JeremyJStarcher/pal1-ram-rom/datasheets/overclocking_pico_files/pico.delta2average.png

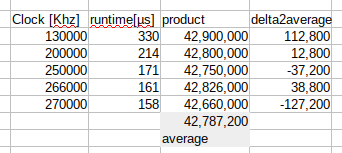
datasheets/overclocking_pico_files/pico.delta2average.png
