JeremyJStarcher/pal1-ram-rom/pics/20240308_011437.jpg

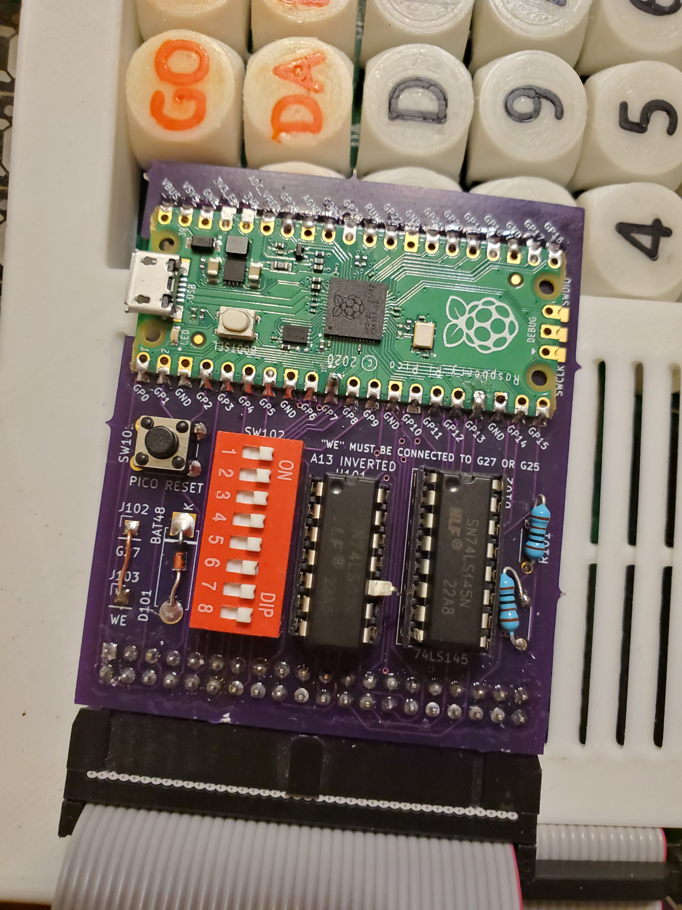
pics/20240308_011437.jpg
