JeremyJStarcher/pal1-ram-rom/datasheets/overclocking_pico_files/mc.performance.png

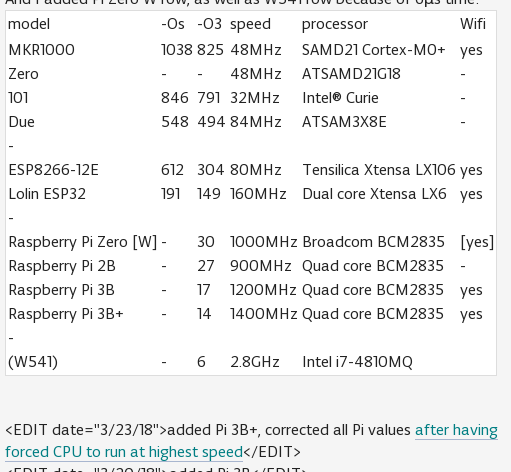
datasheets/overclocking_pico_files/mc.performance.png
