JeremyJStarcher/pal1-ram-rom/src/pal-expansion/commands.c

#include "commands.h"

#include <ctype.h>
#include <hardware/clocks.h>
#include <hardware/flash.h>
#include <hardware/sync.h>
#include <hardware/timer.h>
#include <malloc.h>
#include <pico/multicore.h>
#include <pico/stdlib.h>
#include <stdarg.h>
#include <stdbool.h>
#include <stdio.h>
#include <stdlib.h>
#include <string.h>
#include <tusb.h>

#include "clockspeed.h"
#include "rambuf.h"
#include "xmodem.h"

#define MEMORY_UNMAPPED 0
#define MEMORY_RAM 1
#define MEMORY_ROM 2
#define MEMORY_IGNORE 3
#define MEMORY_UNKNOWN 4

#define MAX_VALID_INDEX ((_flash_size / 2) / sizeof(SysStateStruct)) - 1

//#define PRINT_DEBUG

#define TOKEN_RAM 1
#define TOKEN_ROM 2
#define TOKEN_UNKNOWN 3

void main_memory_loop(void);

unsigned long _xip_base;
unsigned long _flash_size;
uint32_t ints;

bool load_ptp_error = false;
bool load_ptp_done = false;

// If the PAL is not responding, stop sending things to it.
bool output_to_pal = true;

#include <stdarg.h>
#include <stdio.h>

void aputchar(char c) {
  putchar(c);

  if (output_to_pal) {
    pokeram(XCH_TO_PAL, c);
    pokeram(XCH_CMD_REG, XCH_CMD_CHOUT);

    absolute_time_t start_time = get_absolute_time();

    while (true) {
      int xch_clk = peekram(XCH_CMD_REG);
      if (xch_clk == XCH_CMD_NONE) {
        break;
      }

      if (absolute_time_diff_us(start_time, get_absolute_time()) >= 500000) {
        output_to_pal = false;
        break;
      }
    }
  }
}

void aputs(char *c) {
  for (int i = 0; i < strlen(c); ++i) {
    aputchar(c[i]);
  }

  aputchar('\r');
  aputchar('\n');
}

// Wrapper function for snaprintf to send formatted string via api_send_char.
int aprintf(const char *format, ...) {
  va_list args;
  va_start(args, format);

  // Assuming a maximum buffer size. Adjust this according to your needs.
  char buffer[1024];
  int formatted_len = vsnprintf(buffer, sizeof(buffer), format, args);
  va_end(args);

  // Check if snaprintf succeeded
  if (formatted_len < 0) {
    return -1;  // Return an error.
  }

  // Send each character of the formatted string via the API.
  for (int i = 0; i < formatted_len; ++i) {
    aputchar(buffer[i]);
  }

  return formatted_len;  // Return the number of characters sent.
}

uint8_t token_ram_rom(char *token) {
  if (strcmp(token, "ROM") == 0) {
    return TOKEN_ROM;
  }

  if (strcmp(token, "RAM") == 0) {
    return TOKEN_RAM;
  }

  return TOKEN_UNKNOWN;
}

void pause() {
  // If the USB is still busy when we enter a critical section,
  // bad things tend to happen, so give time for the USB bursts to
  // to through.

  volatile long long i;
  long long count = 1 * 10000000;

  for (i = 0; i < count; i++) {
    // Empty loop body
  }
}

uintptr_t get_offset(size_t index) {
  // Assuming you want the size of the structure
  size_t size = sizeof(SysStateStruct);
  return (_flash_size / 2) + (index * size);
}

bool is_safe_to_access(size_t index) {
  if (index > MAX_VALID_INDEX) {
    return false;  // Index is out of valid range
  }

  uintptr_t offset = get_offset(index);
  uintptr_t end_address = XIP_BASE + offset + sizeof(SysStateStruct);
  // Check if end address exceeds flash size or other boundary conditions
  if (end_address > XIP_BASE + _flash_size) {
    return false;
  }

  // Add any additional checks for alignment here if necessary
  // For example, if your system requires 4-byte alignment:
  if ((XIP_BASE + offset) % (4 * 1024) != 0) {
    return false;  // Address is not properly aligned
  }

  return true;  // Safe to access
}

SysStateStruct *get_slot_ptr(size_t index) {
  if (!is_safe_to_access(index)) {
    aprintf("Error: Unsafe to access the requested memory slot.\r\n");
    return NULL;  // Use NULL for pointer error signaling
  }

  size_t size = sizeof(SysStateStruct);
  uintptr_t offset = get_offset(index);

  // Correctly cast and return the pointer
  return (SysStateStruct *)(XIP_BASE + offset);
}

void load_slot_command(char *token) {
  char *param_str =
      strtok(NULL, " ");  // Try to get the next word as a parameter
  int index = -1;         // Default index value if no parameter is provided
  if (param_str == NULL) {
    aputs("NO SLOT NUMBER GIVEN");
  }
  // index = atoi(param_str); // Convert parameter string to integer
  index = (uint8_t)strtol(param_str, NULL, 16);

  memcpy(&sys_state, get_slot_ptr(index), sizeof(SysStateStruct));
}
void crit_start() {
  pause();
  multicore_reset_core1();
  ints = save_and_disable_interrupts();
  set_sys_clock_khz(CLOCK_SPEED_LOW, false);
}

void crit_end() {
  restore_interrupts(ints);
  multicore_launch_core1(main_memory_loop);
  set_sys_clock_khz(CLOCK_SPEED_HIGH, false);
  pause();
}

uint16_t parse_word_from_string(char *line) {
  char temp_s[5];
  temp_s[0] = line[0];
  temp_s[1] = line[1];
  temp_s[2] = line[2];
  temp_s[3] = line[3];
  temp_s[4] = 0;

  return (uint16_t)strtol(temp_s, NULL, 16);
}

uint8_t parse_byte_from_string(char *line) {
  char temp_s[5];

  temp_s[0] = line[0];
  temp_s[1] = line[1];
  temp_s[2] = 0;

  return (uint8_t)strtol(temp_s, NULL, 16);
}

void start_ptp_load(void) {
  load_ptp_error = false;
  load_ptp_done = false;
}

bool load_ptp_line(char *line) {
  int idx = 0;
  uint16_t addr;
  int count;
  uint8_t data;

  uint16_t checksum = 0;
  uint16_t given_checksum = 0;

  // Skip blank/short lines.
  if (strlen(line) < 5) {
    return true;
  }

  // Search until we find the starting ';'
  while (line[idx] != ';') {
    idx += 1;
  }

  // Skip the ';'
  idx += 1;

  // Convert hex string to number
  count = parse_byte_from_string(&line[idx]);
  if (count == 0) {
    load_ptp_done = true;
    return true;
  }

  checksum += count;

  // skip the count
  idx += 2;

  addr = parse_word_from_string(&line[idx]);
  checksum += (int)addr / 256;
  checksum += (int)addr % 256;

  // And skip the address
  idx += 4;

  while (count > 0) {
    data = parse_byte_from_string(&line[idx]);
    checksum += data;
    idx += 2;
    count--;

    pokeram(addr, data);
    addr += 1;
  }

  given_checksum = parse_word_from_string(&line[idx]);

  if (given_checksum == checksum) {
    return true;
  }

  load_ptp_error = true;
  return false;
}

/*****/

void read_string(char *buffer, int max_length) {
  int count = 0;  // Number of characters currently in the buffer
  int ch;         // Character read from stdin

  while (1) {
    // jjz

    pokeram(XCH_CMD_REG, XCH_CMD_CHIN);
    pokeram(XCH_FROM_PAL, 0);

    ch = getchar_timeout_us(10);
    if (ch == -1) {
      ch = peekram(XCH_FROM_PAL);
      if (ch == 0) {
        continue;
      }
      output_to_pal = true;
    }

    ch = toupper(ch);

    if (ch == '\n' || ch == '\r') {
      break;
    }

    // Handle backspace ('\b' or ASCII 127)
    if ((ch == '\b' || ch == 127) && count > 0) {
      // Remove the last character from the buffer
      count--;
      // Echo backspace sequence to terminal (backspace, space, backspace)
      aputchar('\b');
      aputchar(' ');
      aputchar('\b');
      continue;
    }

    // In the printable range?
    if (ch >= 32 && ch <= 126) {
      // If the buffer is not full, add the character to the buffer
      if (count < max_length - 1) {
        buffer[count++] = ch;
        aputchar(ch);  // Echo the character
      }
    }
  }

  // Null-terminate the string
  buffer[count] = '\0';
  pokeram(XCH_CMD_REG, XCH_CMD_NONE);
}

void command_help() {
  aprintf("---- HELP ----- \r\n");
  aprintf("L: Load a paper tape file \r\n");
  aprintf("MSB: FILL ROM WITH MSB (USED TO VERIFY ADDRESS CODING)\r\n");
  aprintf("LSB: FILL ROM WITH LSB (USED TO VERIFY ADDRESS CODING)\r\n");
  aprintf("RESET: RESET RAM/ROM TO POWERUP STATE\r\n");
  aprintf("SAVE #: SAVE TO A SLOT IN FLASH MEMORY\r\n");
  aprintf("LOAD #: LOAD FROM A SLOT IN FLASH MEMORY\r\n");
  aprintf("LIST: LIST CONFIGURATIONS TO LOAD\r\n");
  aprintf("RX [RAM|ROM] ####: RECEIVE XMODEM\r\n");
  aprintf("MEMMAP: SHOW A MEMORY MAP\r\n");
  aprintf(
      "POKE|DPOKE [RAM|ROM] ADDR VALUE: POKE A BYTE OR WORD TO AN ADDRESS\r\n");
  aprintf("PEEK|DPEEK ADDR: PEEK A A BYTE OR WORD\r\n");
  // aprintf("PAUSE: PAUSE DEMO\r\n");
}

void command_fill_ram_msb() {
  uint16_t addr;
  uint8_t data;
  for (addr = 0x2000; addr < 0xFFF0; addr += 1) {
    data = addr / 256;
    pokeram(addr, data);
  }
}

void command_fill_ram_lsb() {
  uint16_t addr;
  uint8_t data;
  for (addr = 0x2000; addr < 0xFFF0; addr += 1) {
    data = addr % 256;
    pokeram(addr, data);
  }
}

void command_loadptp() {
  char input[200];  // Define the buffer size

  start_ptp_load();

  while (!load_ptp_done) {
    read_string(input, sizeof(input));
    load_ptp_line(input);
  }

  if (load_ptp_error) {
    aprintf("*ERR*");
  } else {
    aprintf("*PAL*");
  }
}

void command_save_slot(char *token) {
  char *param_str =
      strtok(NULL, " ");  // Try to get the next word as a parameter
  int index = -1;         // Default index value if no parameter is provided
  if (param_str != NULL) {
    // index = atoi(param_str); // Convert parameter string to integer
    index = (uint8_t)strtol(param_str, NULL, 16);

  } else {
    aprintf("MUST SPECIFY AN INDEX NUMBER\r\n");
    return;
  }

  if (!is_safe_to_access(index)) {
    aprintf("Error: Unsafe to access the requested memory slot.\r\n");
    aprintf("ONLY SLOTS %02x to %02x MAY BE USED\r\n", 0, MAX_VALID_INDEX);
    return;  // Exit or handle error appropriately
  }

  size_t size =
      sizeof(SysStateStruct);  // Assuming you want the size of the structure
  uintptr_t offset = get_offset(index);

#ifdef PRINT_DEBUG
  aprintf("FLASH SIZE: %08x\r\n", _flash_size);
  aprintf("SAVE SLOT: %d OFFSET %04x  size: %08x\r\n", index, offset, size);
  if (offset % 4096 == 0) {
    aprintf("ON THE BOUNDARY\r\n");
  } else {
    aprintf("OOPS\r\n");
  }
#endif

  aputs("OLD DESCRIPTION OF SAVE SLOT: ");
  SlotStateStruct slot_state;
  get_slot_state(index, &slot_state);
  aputs(slot_state.description);

  char input[SYS_DESCRIPTION_SIZE];
  aputs("ENTER NEW DESCRIPTION OR BLANK TO ABORT: ");
  read_string(input, sizeof(input));
  aputs("");

  if (strlen(input) == 0) {
    aputs("BLANK DESCRIPTION: ABORTING");
    return;
  }

  aputs("SAVING TO FLASH. THIS WILL TAKE A FEW SECONDS.");
  aputs("WILL NEED TO RESET YOUR PAL-1 AFTER THIS");
  scpy(sys_state.description, input, SYS_DESCRIPTION_SIZE);

  pause();
  size_t idx = offset;

  crit_start();
  flash_range_erase(idx, size);
  flash_range_program(offset, (char *)&sys_state, size);
  crit_end();
}

void get_slot_state(size_t i, SlotStateStruct *slot_state) {
  char flag[] = MAGIC_PRIMED_KEY;
  SysStateStruct *state = get_slot_ptr(i);

  unsigned int c0 = state->primed_flag[0];
  unsigned int c1 = state->primed_flag[1];
  unsigned int c2 = state->primed_flag[2];
  unsigned int c3 = state->primed_flag[3];

  bool pass = true;

  if (c0 != flag[0]) {
    pass = false;
  }
  if (c1 != flag[1]) {
    pass = false;
  }
  if (c2 != flag[2]) {
    pass = false;
  }
  if (c3 != flag[3]) {
    pass = false;
  }

  slot_state->primed = pass;

  if (pass) {
    scpy(slot_state->description, state->description, SYS_DESCRIPTION_SIZE);
  } else {
    scpy(slot_state->description, "<unset>", SYS_DESCRIPTION_SIZE);
  }
}

void command_list_slots() {
  for (size_t i = 0; i < MAX_VALID_INDEX; i++) {
    aprintf("SLOT: %02x ", i);

    SlotStateStruct slot_state;
    get_slot_state(i, &slot_state);

    aputs(slot_state.description);
  }
}

void command_poke(char *token) {
  uint16_t addr;
  uint16_t data;
  bool dpoke = (strcmp(token, "DPOKE") == 0);

  token = strtok(NULL, " ");

  uint8_t dest_type = token_ram_rom(token);
  if (dest_type == TOKEN_UNKNOWN) {
    aprintf("MUST SPECIFY RAM/ROM\r\n");
    return;
  }

  token = strtok(NULL, " ");

  if (strlen(token) == 0) {
    aprintf("MUST SPECIFY ADDRESS\r\n");
    return;
  }

  addr = (uint16_t)strtol(token, NULL, 16);

  token = strtok(NULL, " ");

  if (strlen(token) == 0) {
    aprintf("MUST SPECIFY VALUE\r\n");
    return;
  }
  data = (uint16_t)strtol(token, NULL, 16);

  if (dpoke) {
    if (dest_type == TOKEN_ROM) {
      dpokerom(addr, data);
    } else {
      dpokeram(addr, data);
    }

  } else {
    if (dest_type == TOKEN_ROM) {
      pokerom(addr, data);
    } else {
      pokeram(addr, data);
    }
  }
}

void command_peek(char *token) {
  uint16_t addr;
  uint16_t data;
  bool dpeek = (strcmp(token, "DPEEK") == 0);

  token = strtok(NULL, " ");

  if (strlen(token) == 0) {
    aprintf("MUST SPECIFY ADDRESS\r\n");
    return;
  }

  addr = (uint16_t)strtol(token, NULL, 16);

  if (dpeek) {
    uint16_t data = dpeekram(addr);
    aprintf("%04X", data);
  } else {
    uint8_t data = peekram(addr);
    aprintf("%02X", data);
  }
}

void command_rx(char *token) {
  aprintf("RX...\r\n");
  uint16_t addr;

  token = strtok(NULL, " ");

  uint8_t dest_type = token_ram_rom(token);
  if (dest_type == TOKEN_UNKNOWN) {
    aprintf("MUST SPECIFY RAM/ROM\n\n");
    return;
  }

  if (dest_type == TOKEN_ROM) {
    aprintf("LOADING AS ROM NOT YET AVAILABLE\r\n");
  }

  token = strtok(NULL, " ");

  if (strlen(token) == 0) {
    aprintf("MUST SPECIFY ADDRESS\r\n");
    return;
  }

  addr = (uint16_t)strtol(token, NULL, 16);

  aprintf("RAM/ROM %s\r\n", dest_type == TOKEN_ROM ? "ROM" : "RAM");
  aprintf("ADDR %04x\r\n", addr);

  UploadConfig dest;
  dest.upload_type = XMODEL_UPLOAD_TYPE_PROGRAM;
  dest.location.base_address = addr;

  xmodemReceive(&dest, 0x4000);
}

uint8_t memory_type(uint16_t addr) {
  uint16_t data = sys_state.memory[addr];

  if (data & (1 << EXCLUDE_BIT)) {
    return MEMORY_IGNORE;
  }

  if (data & (1 << RO_MEMORY_BIT)) {
    return MEMORY_ROM;
  }

  if (data & (1 << IN_USE_BIT)) {
    return MEMORY_RAM;
  }

  return MEMORY_UNMAPPED;
}

void print_memmap_range(uint16_t start_addr, uint16_t idx, uint8_t mem_type) {
  aprintf("%04x::%04x ", start_addr, idx);

  switch (mem_type) {
    case MEMORY_UNMAPPED:
      aprintf("NOT MAPPED");
      break;
    case MEMORY_RAM:
      aprintf("RAM");
      break;
    case MEMORY_ROM:
      aprintf("ROM");
      break;
    case MEMORY_IGNORE:
      aprintf("IGNORED");
      break;
    case MEMORY_UNKNOWN:
      aprintf("UNKNOWN");
      break;
  }

  aprintf("\r\n");
}

void command_memmap(void) {
  uint8_t mem_type;
  uint16_t start_addr = 0x0000;
  uint8_t start_mem_type = memory_type(start_addr);
  size_t idx;

  for (idx = 0x0000; idx < 0xFFFF; idx++) {
    mem_type = memory_type(idx);

    if (mem_type != start_mem_type) {
      print_memmap_range(start_addr, idx - 1, start_mem_type);
      start_addr = idx;
      start_mem_type = mem_type;
    }
  }
  print_memmap_range(start_addr, 0xFFFF, start_mem_type);
}

void command_loop(unsigned long xip_base, unsigned long flash_size) {
  char input[20];  // Define the buffer size

  _xip_base = xip_base;
  _flash_size = flash_size;

  while (1) {
    aprintf("\r\nENTER COMMAND (OR HELP): ");
    read_string(input, sizeof(input));
    // aprintf("\r\nYou entered: %s\r\n", input);

    char *command = strtok(input, " ");  // Get the first word as the command
    if (command == NULL) {
      continue;  // If no command is entered, skip to the next iteration
    }

    aprintf("\r\n");

    // Compare input with known commands and call the corresponding function
    if (strcmp(command, "HELP") == 0) {
      command_help();
    } else if (strcmp(command, "PAUSE") == 0) {
      aputs("LINE 1 - PAUSING");
      pause();
      aputs("LINE 2 - PAUSING");
      pause();
    } else if (strcmp(command, "MEMMAP") == 0) {
      command_memmap();
    } else if (strcmp(command, "L") == 0) {
      command_loadptp();
    } else if (strcmp(command, "LSB") == 0) {
      command_fill_ram_lsb();
    } else if (strcmp(command, "MSB") == 0) {
      command_fill_ram_msb();
    } else if (strcmp(command, "RESET") == 0) {
      setup_memory_contents();
    } else if (strcmp(command, "SAVE") == 0) {
      command_save_slot(command);
    } else if (strcmp(command, "LOAD") == 0) {
      load_slot_command(command);
    } else if (strcmp(command, "LIST") == 0) {
      command_list_slots();
    } else if (strcmp(command, "RX") == 0) {
      command_rx(command);
    } else if (strcmp(command, "POKE") == 0) {
      command_poke(command);
    } else if (strcmp(command, "DPOKE") == 0) {
      command_poke(command);
    } else if (strcmp(command, "DPEEK") == 0) {
      command_peek(command);
    } else if (strcmp(command, "PEEK") == 0) {
      command_peek(command);
    } else if (strcmp(command, "") == 0) {
      // ignore it.
    } else {
      aprintf("HUH?\r\n");
    }
  }
}

void print_binary(unsigned int value, int bits) {
  unsigned int mask =
      1 << (bits - 1);  // Create a mask for the most significant bit

  for (int i = 0; i < bits; i++) {
    aputchar((value & mask) ? '1' : '0');  // Check if the current bit is set

    if ((i + 1) % 4 == 0) {
      aputchar('_');  // Check if the current bit is set
    }

    value <<= 1;  // Shift the value left to check the next bit
  }
}
