JeremyJStarcher/pal1-ram-rom/src/pal-expansion/data.c

#include <stdio.h>
#include <stdlib.h>

void setbyte(uint32_t address, uint8_t value);

static int16_t binary[] = {

    0x4C, 0x0F, 0xA0, 0x4C, 0x32, 0xA0, 0x4C, 0x60, 0xA0, 0x4C, 0xF7, 0xA1,
    0x4C, 0x54, 0xA4, 0xD8, 0xA2, 0xFF, 0x9A, 0xA9, 0x1C, 0x85, 0xE0, 0xA9,
    0xA1, 0x85, 0xE1, 0x20, 0x0A, 0xA1, 0xA9, 0x36, 0x85, 0xE0, 0xA9, 0xA1,
    0x85, 0xE1, 0x20, 0x0A, 0xA1, 0x20, 0x5A, 0x1E, 0x29, 0x5F, 0xC9, 0x42,
    0xD0, 0x2A, 0xD8, 0xA9, 0x66, 0x85, 0xE0, 0xA9, 0xA1, 0x85, 0xE1, 0x20,
    0x0A, 0xA1, 0xA9, 0xDA, 0x85, 0xE0, 0xA9, 0xA4, 0x85, 0xE1, 0xA9, 0x4A,
    0x85, 0xE2, 0xA9, 0xC7, 0x85, 0xE3, 0xA9, 0x00, 0x85, 0xE4, 0xA9, 0x20,
    0x85, 0xE5, 0x20, 0xB9, 0xA0, 0x4C, 0x65, 0x40, 0xC9, 0x46, 0xD0, 0x2B,
    0xD8, 0xA9, 0x7F, 0x85, 0xE0, 0xA9, 0xA1, 0x85, 0xE1, 0x20, 0x0A, 0xA1,
    0xA9, 0x4A, 0x85, 0xE0, 0xA9, 0xC7, 0x85, 0xE1, 0xA9, 0xE9, 0x85, 0xE2,
    0xA9, 0xDF, 0x85, 0xE3, 0xA9, 0x00, 0x85, 0xE4, 0xA9, 0x23, 0x85, 0xE5,
    0x20, 0xB9, 0xA0, 0xD8, 0x4C, 0x00, 0x23, 0xC9, 0x5A, 0xD0, 0x0E, 0xA9,
    0x99, 0x85, 0xE0, 0xA9, 0xA1, 0x85, 0xE1, 0x20, 0x0A, 0xA1, 0x4C, 0xF7,
    0xA1, 0xC9, 0x4D, 0xD0, 0x0E, 0xA9, 0xB6, 0x85, 0xE0, 0xA9, 0xA1, 0x85,
    0xE1, 0x20, 0x0A, 0xA1, 0x4C, 0x54, 0xA4, 0xC9, 0x58, 0xF0, 0x03, 0x4C,
    0x1E, 0xA0, 0x4C, 0x4F, 0x1C, 0xA0, 0x00, 0xB1, 0xE0, 0x91, 0xE4, 0xA5,
    0xE1, 0xC5, 0xE3, 0xD0, 0x07, 0xA5, 0xE0, 0xC5, 0xE2, 0xD0, 0x01, 0x60,
    0xE6, 0xE0, 0xD0, 0x02, 0xE6, 0xE1, 0xE6, 0xE4, 0xD0, 0x02, 0xE6, 0xE5,
    0x4C, 0xBB, 0xA0, 0x98, 0x85, 0xE1, 0xAD, 0x42, 0x17, 0x29, 0xFE, 0x8D,
    0x42, 0x17, 0x20, 0x5A, 0x1E, 0x85, 0xE0, 0xAD, 0x42, 0x17, 0x09, 0x01,
    0x8D, 0x42, 0x17, 0xA5, 0xE1, 0xA8, 0xA5, 0xE0, 0x60, 0x98, 0x85, 0xE1,
    0xA9, 0x0D, 0x20, 0xA0, 0x1E, 0xA9, 0x0A, 0x20, 0xA0, 0x1E, 0xA5, 0xE1,
    0xA8, 0x60, 0xA0, 0x00, 0xB1, 0xE0, 0xF0, 0x0B, 0x20, 0xA0, 0x1E, 0xE6,
    0xE0, 0xD0, 0xF3, 0xE6, 0xE1, 0xD0, 0xEF, 0x60, 0x0D, 0x0A, 0x50, 0x41,
    0x4C, 0x2D, 0x31, 0x20, 0x52, 0x4F, 0x4D, 0x20, 0x4C, 0x6F, 0x61, 0x64,
    0x65, 0x72, 0x20, 0x76, 0x31, 0x2E, 0x30, 0x0D, 0x0A, 0x00, 0x0D, 0x0A,
    0x28, 0x42, 0x29, 0x41, 0x53, 0x49, 0x43, 0x2C, 0x20, 0x28, 0x46, 0x29,
    0x4F, 0x52, 0x54, 0x48, 0x2C, 0x20, 0x65, 0x57, 0x6F, 0x28, 0x7A, 0x29,
    0x20, 0x4D, 0x6F, 0x6E, 0x69, 0x74, 0x6F, 0x72, 0x2C, 0x20, 0x6F, 0x72,
    0x20, 0x65, 0x28, 0x58, 0x29, 0x69, 0x74, 0x3F, 0x20, 0x00, 0x0D, 0x0A,
    0x53, 0x74, 0x61, 0x72, 0x74, 0x69, 0x6E, 0x67, 0x20, 0x4D, 0x53, 0x20,
    0x42, 0x41, 0x53, 0x49, 0x43, 0x2E, 0x2E, 0x2E, 0x0D, 0x0A, 0x00, 0x0D,
    0x0A, 0x53, 0x74, 0x61, 0x72, 0x74, 0x69, 0x6E, 0x67, 0x20, 0x46, 0x49,
    0x47, 0x20, 0x46, 0x4F, 0x52, 0x54, 0x48, 0x2E, 0x2E, 0x2E, 0x0D, 0x0A,
    0x00, 0x0D, 0x0A, 0x53, 0x74, 0x61, 0x72, 0x74, 0x69, 0x6E, 0x67, 0x20,
    0x65, 0x57, 0x6F, 0x7A, 0x20, 0x4D, 0x6F, 0x6E, 0x69, 0x74, 0x6F, 0x72,
    0x2E, 0x2E, 0x2E, 0x0D, 0x0A, 0x00, 0x0D, 0x0A, 0x43, 0x6F, 0x70, 0x79,
    0x69, 0x6E, 0x67, 0x20, 0x6D, 0x65, 0x6D, 0x6F, 0x72, 0x79, 0x20, 0x74,
    0x65, 0x73, 0x74, 0x20, 0x28, 0x66, 0x72, 0x6F, 0x6D, 0x20, 0x46, 0x69,
    0x72, 0x73, 0x74, 0x20, 0x42, 0x6F, 0x6F, 0x6B, 0x20, 0x6F, 0x66, 0x20,
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

void set_values(void) {
  uint16_t base = 0x0000;
  int16_t data;

  while (true) {
    data = binary[base];
    printf("%d \n", data);
    if (data == -1) {
      break;
    }
    setbyte(0xA000 + base, data);
    base += 1;
  }
}
