JeremyJStarcher/pal1-ram-rom/src/pal-expansion/rom_ext.c

unsigned char rom_ext[] = {
    0x4C, 0x00, 0xB3, 0x4C, 0x0E, 0xB3, 0x10, 0xFB, 0xAD, 0x10, 0xD0, 0x60,
    0x8A, 0x29, 0x20, 0xF0, 0x23, 0xA9, 0xA0, 0x85, 0xE4, 0x4C, 0xC9, 0xA3,
    0xA9, 0x20, 0xC5, 0x24, 0xB0, 0x0C, 0xA9, 0x8D, 0xA0, 0x07, 0x20, 0xC9,
    0xA3, 0xA9, 0xA0, 0x88, 0xD0, 0xF8, 0xA0, 0x00, 0xB1, 0xE2, 0xE6, 0xE2,
    0xD0, 0x02, 0xE6, 0xE3, 0x60, 0x20, 0x15, 0xA7, 0x20, 0x76, 0xA5, 0xA5,
    0xE2, 0xC5, 0xE6, 0xA5, 0xE3, 0xE5, 0xE7, 0xB0, 0xEF, 0x20, 0x6D, 0xA0,
    0x4C, 0x3B, 0xA0, 0xA5, 0xCA, 0x85, 0xE2, 0xA5, 0xCB, 0x85, 0xE3, 0xA5,
    0x4C, 0x85, 0xE6, 0xA5, 0x4D, 0x85, 0xE7, 0xD0, 0xDE, 0x20, 0x15, 0xA7,
    0x20, 0x6D, 0xA5, 0xA5, 0xE4, 0x85, 0xE2, 0xA5, 0xE5, 0x85, 0xE3, 0xB0,
    0xC7, 0x86, 0xD8, 0xA9, 0xA0, 0x85, 0xFA, 0x20, 0x2A, 0xA0, 0x98, 0x85,
    0xE4, 0x20, 0x2A, 0xA0, 0xAA, 0x20, 0x2A, 0xA0, 0x20, 0x1B, 0xA5, 0x20,
    0x18, 0xA0, 0x84, 0xFA, 0xAA, 0x10, 0x18, 0x0A, 0x10, 0xE9, 0xA5, 0xE4,
    0xD0, 0x03, 0x20, 0x11, 0xA0, 0x8A, 0x20, 0xC9, 0xA3, 0xA9, 0x25, 0x20,
    0x1A, 0xA0, 0xAA, 0x30, 0xF5, 0x85, 0xE4, 0xC9, 0x01, 0xD0, 0x05, 0xA6,
    0xD8, 0x4C, 0xCD, 0xA3, 0x48, 0x84, 0xCE, 0xA2, 0xAD, 0x86, 0xCF, 0xC9,
    0x51, 0x90, 0x04, 0xC6, 0xCF, 0xE9, 0x50, 0x48, 0xB1, 0xCE, 0xAA, 0x88,
    0xB1, 0xCE, 0x10, 0xFA, 0xE0, 0xC0, 0xB0, 0x04, 0xE0, 0x00, 0x30, 0xF2,
    0xAA, 0x68, 0xE9, 0x01, 0xD0, 0xE9, 0x24, 0xE4, 0x30, 0x03, 0x20, 0xF8,
    0xAF, 0xB1, 0xCE, 0x10, 0x10, 0xAA, 0x29, 0x3F, 0x85, 0xE4, 0x18, 0x69,
    0xA0, 0x20, 0xC9, 0xA3, 0x88, 0xE0, 0xC0, 0x90, 0xEC, 0x20, 0x0C, 0xA0,
    0x68, 0xC9, 0x5D, 0xF0, 0xA4, 0xC9, 0x28, 0xD0, 0x8A, 0xF0, 0x9E, 0x20,
    0x18, 0xA1, 0x95, 0x50, 0xD5, 0x78, 0x90, 0x11, 0xA0, 0x2B, 0x4C, 0xE0,
    0xA3, 0x20, 0x34, 0xAE, 0xD5, 0x50, 0x90, 0xF4, 0x20, 0xE4, 0xAF, 0x95,
    0x78, 0x4C, 0x23, 0xA8, 0x20, 0x34, 0xAE, 0xF0, 0xE7, 0x38, 0xE9, 0x01,
    0x60, 0x20, 0x18, 0xA1, 0x95, 0x50, 0x18, 0xF5, 0x78, 0x4C, 0x02, 0xA1,
    0xA0, 0x14, 0xD0, 0xD6, 0x20, 0x18, 0xA1, 0xE8, 0xB5, 0x50, 0x85, 0xDA,
    0x65, 0xCE, 0x48, 0xA8, 0xB5, 0x78, 0x85, 0xDB, 0x65, 0xCF, 0x48, 0xC4,
    0xCA, 0xE5, 0xCB, 0xB0, 0xE3, 0xA5, 0xDA, 0x69, 0xFE, 0x85, 0xDA, 0xA9,
    0xFF, 0xA8, 0x65, 0xDB, 0x85, 0xDB, 0xC8, 0xB1, 0xDA, 0xD9, 0xCC, 0x00,
    0xD0, 0x0F, 0x98, 0xF0, 0xF5, 0x68, 0x91, 0xDA, 0x99, 0xCC, 0x00, 0x88,
    0x10, 0xF7, 0xE8, 0x60, 0xEA, 0xA0, 0x80, 0xD0, 0x95, 0xA9, 0x00, 0x20,
    0x0A, 0xA7, 0xA0, 0x02, 0x94, 0x78, 0x20, 0x0A, 0xA7, 0xA9, 0xBF, 0x20,
    0xC9, 0xA3, 0xA0, 0x00, 0x20, 0x9E, 0xA2, 0x94, 0x78, 0xEA, 0xEA, 0xEA,
    0xB5, 0x51, 0x85, 0xCE, 0xB5, 0x79, 0x85, 0xCF, 0xE8, 0xE8, 0x20, 0xBC,
    0xA1, 0xB5, 0x4E, 0xD5, 0x76, 0xB0, 0x15, 0xF6, 0x4E, 0xA8, 0xB1, 0xCE,
    0xB4, 0x50, 0xC4, 0xE4, 0x90, 0x04, 0xA0, 0x83, 0xD0, 0xC1, 0x91, 0xDA,
    0xF6, 0x50, 0x90, 0xE5, 0xB4, 0x50, 0x8A, 0x91, 0xDA, 0xE8, 0xE8, 0x60,
    0xB5, 0x51, 0x85, 0xDA, 0x38, 0xE9, 0x02, 0x85, 0xE4, 0xB5, 0x79, 0x85,
    0xDB, 0xE9, 0x00, 0x85, 0xE5, 0xA0, 0x00, 0xB1, 0xE4, 0x18, 0xE5, 0xDA,
    0x85, 0xE4, 0x60, 0xB5, 0x53, 0x85, 0xCE, 0xB5, 0x7B, 0x85, 0xCF, 0xB5,
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
unsigned int rom_extSize = 16384;
