JeremyJStarcher/pal1-ram-rom/src/pal-expansion/ilink.c

unsigned char ilink[] = {
    0x4C, 0xA2, 0x1A, 0x20, 0xCB, 0x1A, 0x48, 0x20, 0xA0, 0x1E, 0x68, 0x60, 0xD8, 0xAD, 0xF9, 0x1F,
    0xC9, 0x01, 0xF0, 0x07, 0xC9, 0x02, 0xF0, 0x0C, 0x4C, 0xA2, 0x1A, 0xAD, 0xF7, 0x1F, 0x20, 0xA0,
    0x1E, 0x4C, 0xC3, 0x1A, 0x20, 0xCB, 0x1A, 0x8D, 0xF8, 0x1F, 0x4C, 0xC3, 0x1A, 0xA9, 0x00, 0x8D,
    0xF9, 0x1F, 0x4C, 0xA2, 0x1A, 0xAD, 0x42, 0x17, 0x29, 0xFE, 0x8D, 0x42, 0x17, 0x20, 0xEC, 0x1A,
    0x48, 0xAD, 0x42, 0x17, 0x09, 0x01, 0x8D, 0x42, 0x17, 0x68, 0xC9, 0x61, 0x90, 0x07, 0xC9, 0x7A,
    0xB0, 0x03, 0x38, 0xE9, 0x20, 0x60, 0x86, 0xFD, 0xA2, 0x08, 0xA9, 0x01, 0x2C, 0x40, 0x17, 0xD0,
    0x22, 0x30, 0xF9, 0x20, 0xD4, 0x1E, 0x20, 0xEB, 0x1E, 0xAD, 0x40, 0x17, 0x29, 0x80, 0x46, 0xFE,
    0x05, 0xFE, 0x85, 0xFE, 0x20, 0xD4, 0x1E, 0xCA, 0xD0, 0xEF, 0x20, 0xEB, 0x1E, 0xA6, 0xFD, 0xA5,
    0xFE, 0x2A, 0x4A, 0x60
};
unsigned int ilinkSize = 132;
