JeremyJStarcher/pal1-ram-rom/src/pal-expansion/pin_definitions.h

// Don't change the pin definitions.
// Optimizations expect that they are in these positions.

// Address pins.
#define A0 0    // 0
#define A1 1    // 1
#define A2 2    // 12
#define A3 3    // 2
#define A4 4    // 3
#define A5 5    // 4
#define A6 6    // 5
#define A7 7    // 6
#define A8 8    // 7
#define A9 9    // 8
#define A10 10  // 9
#define A11 11  // 10
#define A12 12  // 11
#define A13 13  // 13
#define A14 14  // 14
#define A15 15  // 15

// Data pins.
#define D0 16
#define D1 17
#define D2 18
#define D3 19
#define D4 20
#define D5 21
#define D6 22
#define D7 26

#define WE 27
#define DEN 28
#define PHI2 25
