JeremyJStarcher/pal1-ram-rom/src/pal-expansion/riottest.c

unsigned char riot_test[] = {
    0x4C, 0x03, 0x02, 0xD8, 0x20, 0x2F, 0x1E, 0x20, 0x2F, 0x1E, 0x20, 0xA1, 0x06, 0x52, 0x55, 0x4E,
    0x4E, 0x49, 0x4E, 0x47, 0x20, 0x52, 0x49, 0x4F, 0x54, 0x20, 0x43, 0x4F, 0x4D, 0x50, 0x41, 0x54,
    0x49, 0x42, 0x49, 0x4C, 0x49, 0x54, 0x59, 0x20, 0x54, 0x45, 0x53, 0x54, 0x21, 0x00, 0x20, 0x2F,
    0x1E, 0x20, 0xA1, 0x06, 0x57, 0x49, 0x54, 0x48, 0x4F, 0x55, 0x54, 0x20, 0x42, 0x55, 0x53, 0x59,
    0x20, 0x4E, 0x4F, 0x4F, 0x50, 0x53, 0x21, 0x00, 0x20, 0x2F, 0x1E, 0x20, 0xA1, 0x06, 0x52, 0x75,
    0x6E, 0x6E, 0x69, 0x6E, 0x67, 0x20, 0x74, 0x65, 0x73, 0x74, 0x20, 0x74, 0x69, 0x6D, 0x65, 0x72,
    0x62, 0x61, 0x73, 0x69, 0x63, 0x74, 0x65, 0x73, 0x74, 0x3A, 0x20, 0x00, 0xA9, 0x17, 0x20, 0x3B,
    0x1E, 0xA9, 0x04, 0x20, 0x3B, 0x1E, 0x20, 0x9E, 0x1E, 0xA9, 0x01, 0x8D, 0x04, 0x17, 0xAD, 0x06,
    0x17, 0x85, 0x02, 0xC9, 0xFD, 0xF0, 0x33, 0x20, 0xA1, 0x06, 0x66, 0x61, 0x69, 0x6C, 0x65, 0x64,
    0x21, 0x20, 0x20, 0x45, 0x78, 0x70, 0x65, 0x63, 0x74, 0x65, 0x64, 0x20, 0x00, 0xA9, 0xFD, 0x20,
    0x3B, 0x1E, 0x20, 0xA1, 0x06, 0x20, 0x61, 0x63, 0x74, 0x75, 0x61, 0x6C, 0x20, 0x00, 0x20, 0x2F,
    0x1E, 0x20, 0x2F, 0x1E, 0x4C, 0x4F, 0x1C, 0x4C, 0xC6, 0x02, 0x20, 0xA1, 0x06, 0x70, 0x61, 0x73,
    0x73, 0x65, 0x64, 0x3A, 0x20, 0x00, 0xA5, 0x02, 0x20, 0x3B, 0x1E, 0x20, 0x2F, 0x1E, 0x20, 0xA1,
    0x06, 0x52, 0x75, 0x6E, 0x6E, 0x69, 0x6E, 0x67, 0x20, 0x74, 0x65, 0x73, 0x74, 0x20, 0x74, 0x69,
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
    0x55, 0x53, 0x59, 0x20, 0x4E, 0x4F, 0x4F, 0x50, 0x53, 0x21, 0x00, 0x20, 0x2F, 0x1E, 0x20, 0xA1,
    0x06, 0x52, 0x75, 0x6E, 0x6E, 0x69, 0x6E, 0x67, 0x20, 0x74, 0x65, 0x73, 0x74, 0x20, 0x74, 0x69,
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
};
unsigned int riot_testSize = 1226;
