JeremyJStarcher/pal1-ram-rom/pics/20240308_011423.jpg

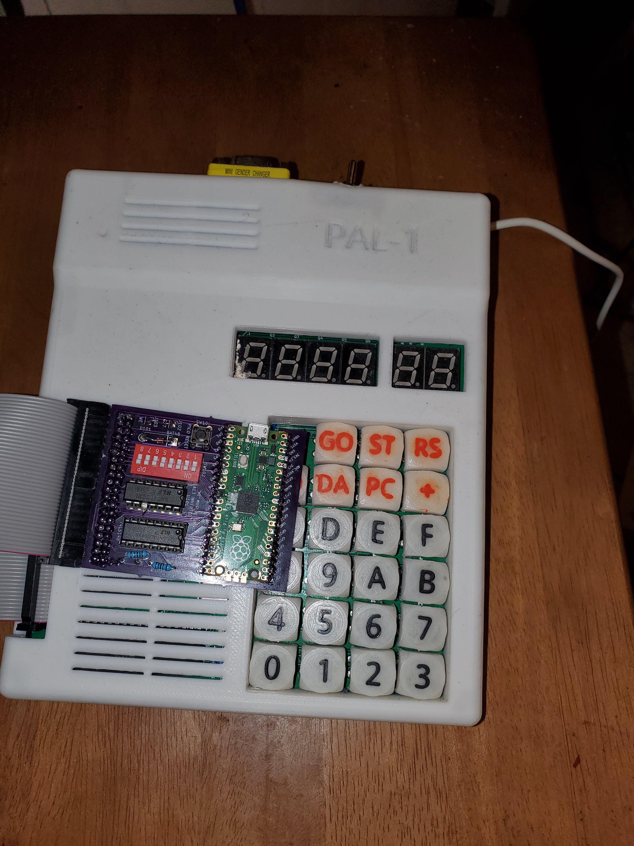
pics/20240308_011423.jpg
